stagehandshawn/EvoFaderWing/include/NeoPixelControl.h

// NeoPixelControl.h
#ifndef NEOPIXEL_CONTROL_H
#define NEOPIXEL_CONTROL_H

#include <Arduino.h>
#include <Adafruit_NeoPixel.h>
#include "Config.h"

//================================
// GLOBAL NEOPIXEL OBJECT
//================================

extern Adafruit_NeoPixel pixels;

//================================
// FUNCTION DECLARATIONS
//================================

// Setup and main update
void setupNeoPixels();
void updateNeoPixels();
void updateBaseBrightnessPixels();
void invalidateNeoPixelRenderCache();

void updateBrightnessOnFaderTouchChange();

void fadeSequence(unsigned long STAGGER_DELAY, unsigned long COLOR_CYCLE_TIME);
void flashAllFadersRed();

uint32_t getScaledColor(const Fader& fader);

#endif // NEOPIXEL_CONTROL_H
